RichCini/LomasBoards/Thunder 186/roms/cm5_src/CM5D.ASM

; Lomas Color Magic specific equates. These are the
; IBM/PC-compatible port addresses.
;
C5TIMER0	equ	40h
C5TIMER1	equ	41h
C5TIMER2	equ	42h
C58253CTL	equ	43h
C58255PA	equ	60h 
C58255PB	equ	61h 
C58255PC	equ	62h
C58255CMD	equ	63h
MC6845R0	equ	03D0h
MC6845R1	equ	03D1h
MC6845R2	equ	03D2h
MC6845R3	equ	03D3h
MC6845R4	equ	03D4h
MC6845R5	equ	03D5h
MC6845R6	equ	03D6h
MC6845R7	equ	03D7h
CGAMODE		equ	03D8h
CGACOLOR	equ	03D9h
CGASTAT		equ	03DAh
LPENCLR		equ	03DBh
LPENSET		equ	03DCh
; 8272 layout, which differs from NEC D765
FDPORT		EQU	03F0H		;BASE PORT ADDRESS FOR CONTROLLER (F0-F7)
FDCS		EQU	FDPORT		;STATUS REGISTER
FDCD		EQU	FDPORT+1	;DATA REGISTER
FDMA		EQU	FDPORT+2	;DMA ADDRESS (WHEN WRITE)
INTS		EQU	FDPORT+2	;STATUS REGISTER (WHEN READ)
; D765 Layout
;FDCP		EQU	FDPORT+2	;Control Port
;INTS		EQU	FDPORT+4	;Main Status Register
;FDCD		EQU	FDPORT+5	;Data Register
